VSmart-Project/vsmart/graphify-out/2026-07-08/GRAPH_REPORT.md

# Graph Report - DATN  (2026-07-08)

## Corpus Check
- 193 files · ~1,565,279 words
- Verdict: corpus is large enough that graph structure adds value.

## Summary
- 1423 nodes · 1795 edges · 120 communities (95 shown, 25 thin omitted)
- Extraction: 98% EXTRACTED · 2% INFERRED · 0% AMBIGUOUS · INFERRED: 42 edges (avg confidence: 0.8)
- Token cost: 0 input · 0 output

## Community Hubs (Navigation)
- [[_COMMUNITY_Backend Auth & Middleware|Backend Auth & Middleware]]
- [[_COMMUNITY_Mobile App Device & Scan|Mobile App Device & Scan]]
- [[_COMMUNITY_Web Frontend Project Config|Web Frontend Project Config]]
- [[_COMMUNITY_Mobile App Dependencies|Mobile App Dependencies]]
- [[_COMMUNITY_Backend Config & Packages|Backend Config & Packages]]
- [[_COMMUNITY_Mobile App Android Resources|Mobile App Android Resources]]
- [[_COMMUNITY_Web Geofencing UI|Web Geofencing UI]]
- [[_COMMUNITY_IoT Message Processor Lambda|IoT Message Processor Lambda]]
- [[_COMMUNITY_Mobile App Geofence Screens|Mobile App Geofence Screens]]
- [[_COMMUNITY_Backend UtilitySimulation Scripts|Backend Utility/Simulation Scripts]]
- [[_COMMUNITY_Backend Anti-Theft Logic|Backend Anti-Theft Logic]]
- [[_COMMUNITY_Web Map Interface Components|Web Map Interface Components]]
- [[_COMMUNITY_Backend Device Controller|Backend Device Controller]]
- [[_COMMUNITY_Web Device Management UI|Web Device Management UI]]
- [[_COMMUNITY_Mobile App Project Config|Mobile App Project Config]]
- [[_COMMUNITY_Mobile App Component|Mobile App Component]]
- [[_COMMUNITY_Backend DynamoDB Services|Backend DynamoDB Services]]
- [[_COMMUNITY_Web Map Interface Components|Web Map Interface Components]]
- [[_COMMUNITY_Mobile App Component|Mobile App Component]]
- [[_COMMUNITY_Web Frontend Component|Web Frontend Component]]
- [[_COMMUNITY_Geofence Event Consumer Lambda|Geofence Event Consumer Lambda]]
- [[_COMMUNITY_Backend UtilitySimulation Scripts|Backend Utility/Simulation Scripts]]
- [[_COMMUNITY_Mobile App Geofence Screens|Mobile App Geofence Screens]]
- [[_COMMUNITY_Mobile App Auth Screens|Mobile App Auth Screens]]
- [[_COMMUNITY_Mobile App Auth Screens|Mobile App Auth Screens]]
- [[_COMMUNITY_Mobile App Navigation Tabs|Mobile App Navigation Tabs]]
- [[_COMMUNITY_Backend Auth & Middleware|Backend Auth & Middleware]]
- [[_COMMUNITY_Offline Detector Lambda|Offline Detector Lambda]]
- [[_COMMUNITY_Backend Location & Geo Services|Backend Location & Geo Services]]
- [[_COMMUNITY_Community 29|Community 29]]
- [[_COMMUNITY_Backend Location & Geo Services|Backend Location & Geo Services]]
- [[_COMMUNITY_Mobile App Navigation Tabs|Mobile App Navigation Tabs]]
- [[_COMMUNITY_Mobile App Component|Mobile App Component]]
- [[_COMMUNITY_Web Layout & Common UI|Web Layout & Common UI]]
- [[_COMMUNITY_Web Map Interface Components|Web Map Interface Components]]
- [[_COMMUNITY_Mobile App Component|Mobile App Component]]
- [[_COMMUNITY_Backend SNS Notifications|Backend SNS Notifications]]
- [[_COMMUNITY_Web Device Management UI|Web Device Management UI]]
- [[_COMMUNITY_Backend UtilitySimulation Scripts|Backend Utility/Simulation Scripts]]
- [[_COMMUNITY_Backend UtilitySimulation Scripts|Backend Utility/Simulation Scripts]]
- [[_COMMUNITY_Realtime Event Publisher Lambda|Realtime Event Publisher Lambda]]
- [[_COMMUNITY_Mobile App Component|Mobile App Component]]
- [[_COMMUNITY_Mobile App Component|Mobile App Component]]
- [[_COMMUNITY_Community 50|Community 50]]
- [[_COMMUNITY_Community 51|Community 51]]
- [[_COMMUNITY_Community 52|Community 52]]
- [[_COMMUNITY_Community 53|Community 53]]
- [[_COMMUNITY_Community 54|Community 54]]
- [[_COMMUNITY_Community 55|Community 55]]
- [[_COMMUNITY_Community 56|Community 56]]
- [[_COMMUNITY_Community 57|Community 57]]
- [[_COMMUNITY_Community 58|Community 58]]
- [[_COMMUNITY_Community 59|Community 59]]
- [[_COMMUNITY_Community 60|Community 60]]
- [[_COMMUNITY_Community 61|Community 61]]
- [[_COMMUNITY_Community 62|Community 62]]
- [[_COMMUNITY_Community 63|Community 63]]
- [[_COMMUNITY_Community 64|Community 64]]
- [[_COMMUNITY_Community 65|Community 65]]
- [[_COMMUNITY_Community 66|Community 66]]
- [[_COMMUNITY_Community 67|Community 67]]
- [[_COMMUNITY_Community 68|Community 68]]
- [[_COMMUNITY_Community 69|Community 69]]
- [[_COMMUNITY_Community 70|Community 70]]
- [[_COMMUNITY_Community 71|Community 71]]
- [[_COMMUNITY_Community 72|Community 72]]
- [[_COMMUNITY_Community 73|Community 73]]
- [[_COMMUNITY_Community 74|Community 74]]
- [[_COMMUNITY_Community 75|Community 75]]
- [[_COMMUNITY_Community 76|Community 76]]
- [[_COMMUNITY_Community 77|Community 77]]
- [[_COMMUNITY_Community 78|Community 78]]
- [[_COMMUNITY_Community 79|Community 79]]
- [[_COMMUNITY_Community 80|Community 80]]
- [[_COMMUNITY_Community 81|Community 81]]
- [[_COMMUNITY_Community 82|Community 82]]
- [[_COMMUNITY_Community 83|Community 83]]
- [[_COMMUNITY_Community 84|Community 84]]
- [[_COMMUNITY_Community 85|Community 85]]
- [[_COMMUNITY_Community 86|Community 86]]
- [[_COMMUNITY_Community 87|Community 87]]
- [[_COMMUNITY_Community 88|Community 88]]
- [[_COMMUNITY_Community 89|Community 89]]
- [[_COMMUNITY_Community 90|Community 90]]
- [[_COMMUNITY_Community 91|Community 91]]
- [[_COMMUNITY_Community 92|Community 92]]
- [[_COMMUNITY_Community 93|Community 93]]
- [[_COMMUNITY_Community 94|Community 94]]
- [[_COMMUNITY_Community 95|Community 95]]
- [[_COMMUNITY_Community 96|Community 96]]
- [[_COMMUNITY_Community 97|Community 97]]
- [[_COMMUNITY_Community 98|Community 98]]
- [[_COMMUNITY_Community 99|Community 99]]
- [[_COMMUNITY_Community 100|Community 100]]
- [[_COMMUNITY_Community 101|Community 101]]
- [[_COMMUNITY_Community 102|Community 102]]
- [[_COMMUNITY_Community 103|Community 103]]
- [[_COMMUNITY_Community 104|Community 104]]
- [[_COMMUNITY_Community 105|Community 105]]
- [[_COMMUNITY_Community 106|Community 106]]
- [[_COMMUNITY_Community 107|Community 107]]
- [[_COMMUNITY_Community 110|Community 110]]
- [[_COMMUNITY_Community 111|Community 111]]
- [[_COMMUNITY_Community 112|Community 112]]
- [[_COMMUNITY_Community 113|Community 113]]
- [[_COMMUNITY_Community 114|Community 114]]
- [[_COMMUNITY_Community 115|Community 115]]
- [[_COMMUNITY_Community 116|Community 116]]
- [[_COMMUNITY_Community 117|Community 117]]
- [[_COMMUNITY_Community 118|Community 118]]

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

## Import Cycles
- 1-file cycle: `vsmart-app/metro.config.js -> vsmart-app/metro.config.js`

## Communities (120 total, 25 thin omitted)

### Community 0 - "Backend Auth & Middleware"
Cohesion: 0.10
Nodes (20): antitheftRoutes, app, {
    APP_EVENTS_TOPIC_TEMPLATE,
    DEBUG_DEVICE_EVENTS_TOPIC_TEMPLATE,
    RAW_TELEMETRY_TOPIC_TEMPLATE,
    REALTIME_EVENT_TYPES,
    REALTIME_SCHEMA_VERSION,
    SAMPLE_REALTIME_EVENTS,
    validateRealtimeEnvelope,
}, authRoutes, cors, deviceRoutes, { errorHandler, notFoundHandler }, express (+12 more)

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

### Community 11 - "Web Map Interface Components"
Cohesion: 0.12
Nodes (13): App(), Toast(), DeviceMarkers(), Header(), menuItems, Sidebar(), DevicesMapOverlay(), STATUS_CONFIG (+5 more)

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

### Community 15 - "Mobile App Component"
Cohesion: 0.22
Nodes (6): requestNotificationPermissions(), showAntitheftAlert(), showDeviceOfflineAlert(), showDeviceOnlineAlert(), showGeofenceAlert(), showLocalNotification()

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

### Community 29 - "Community 29"
Cohesion: 0.28
Nodes (5): createRealtimeEvent(), isObject(), REALTIME_EVENT_TYPES, SAMPLE_REALTIME_EVENTS, validateRealtimeEnvelope()

### Community 30 - "Backend Location & Geo Services"
Cohesion: 0.22
Nodes (3): {
    ListDevicePositionsCommand,
    BatchDeleteDevicePositionHistoryCommand,
    GetDevicePositionHistoryCommand,
}, { LOCATION_TRACKER_NAME }, { locationClient }

### Community 31 - "Mobile App Navigation Tabs"
Cohesion: 0.29
Nodes (3): CustomTabBar(), s, TABS

### Community 32 - "Mobile App Component"
Cohesion: 0.29
Nodes (6): compilerOptions, paths, strict, extends, include, @/*

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

### Community 34 - "Web Map Interface Components"
Cohesion: 0.50
Nodes (4): DeviceHistoryPathLayer(), getDistanceKm(), historyLineLayer, historyPointsLayer

### Community 35 - "Mobile App Component"
Cohesion: 0.40
Nodes (4): Colors, FontSize, Radius, Spacing

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

### Community 61 - "Community 61"
Cohesion: 0.33
Nodes (6): scripts, android, ios, lint, start, web

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

### Community 90 - "Community 90"
Cohesion: 0.33
Nodes (3): { CognitoJwtVerifier }, requireAuth(), AuthLayout()

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

### Community 99 - "Community 99"
Cohesion: 0.50
Nodes (3): options, swaggerJSDoc, swaggerSpec

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

### Community 107 - "Community 107"
Cohesion: 0.50
Nodes (3): deviceController, express, router

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

## Knowledge Gaps
- **730 isolated node(s):** `solutionid_validator.sh script`, `name`, `private`, `version`, `type` (+725 more)
  These have ≤1 connection - possible missing edges or undocumented components.
- **25 thin communities (<3 nodes) omitted from report** — run `graphify query` to explore isolated nodes.

## Suggested Questions
_Questions this graph is uniquely positioned to answer:_

- **Why does `millis()` connect `Web Layout & Common UI` to `Community 70`, `Community 84`, `Community 86`, `Community 91`, `Community 92`, `Community 93`?**
  _High betweenness centrality (0.112) - this node is a cross-community bridge._
- **Why does `TinyGPSLocation` connect `Community 86` to `Community 82`, `Community 70`?**
  _High betweenness centrality (0.085) - this node is a cross-community bridge._
- **What connects `solutionid_validator.sh script`, `name`, `private` to the rest of the system?**
  _735 weakly-connected nodes found - possible documentation gaps or missing edges._
- **Should `Backend Auth & Middleware` be split into smaller, more focused modules?**
  _Cohesion score 0.09956709956709957 - nodes in this community are weakly interconnected._
- **Should `Web Frontend Project Config` be split into smaller, more focused modules?**
  _Cohesion score 0.05263157894736842 - nodes in this community are weakly interconnected._
- **Should `Mobile App Dependencies` be split into smaller, more focused modules?**
  _Cohesion score 0.05405405405405406 - nodes in this community are weakly interconnected._
- **Should `Backend Config & Packages` be split into smaller, more focused modules?**
  _Cohesion score 0.05555555555555555 - nodes in this community are weakly interconnected._
